doomsquadairsoft/d3vice-controlpoint-xbee/other/pics/guts.jpg

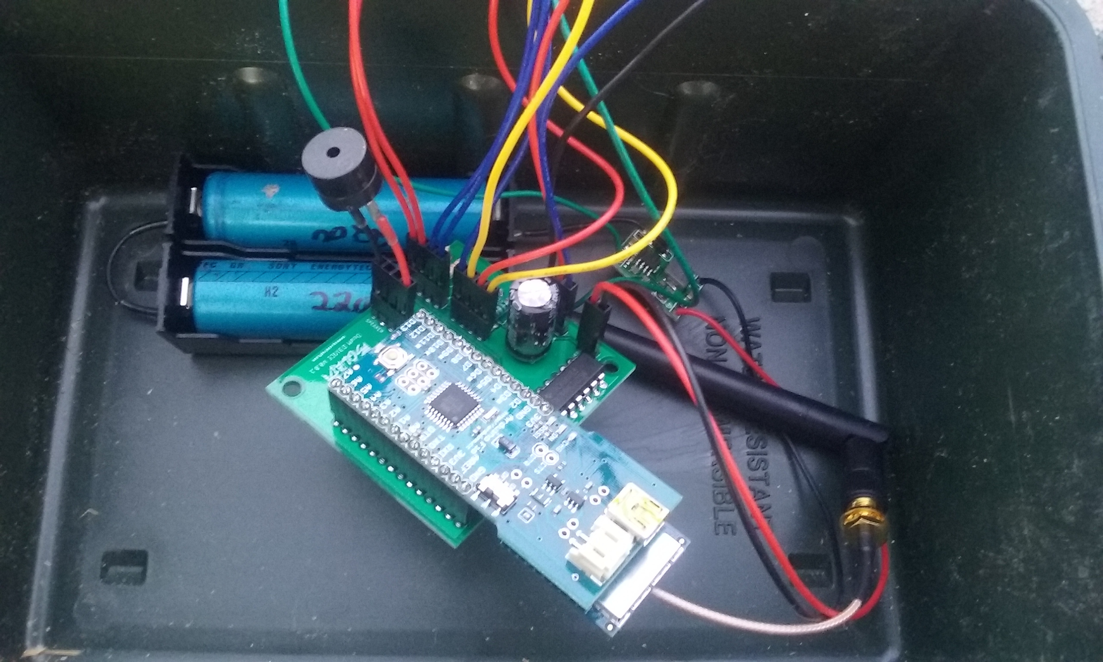
other/pics/guts.jpg
