doomsquadairsoft/d3vice-controlpoint-xbee/other/pics/pcb_yadda.png

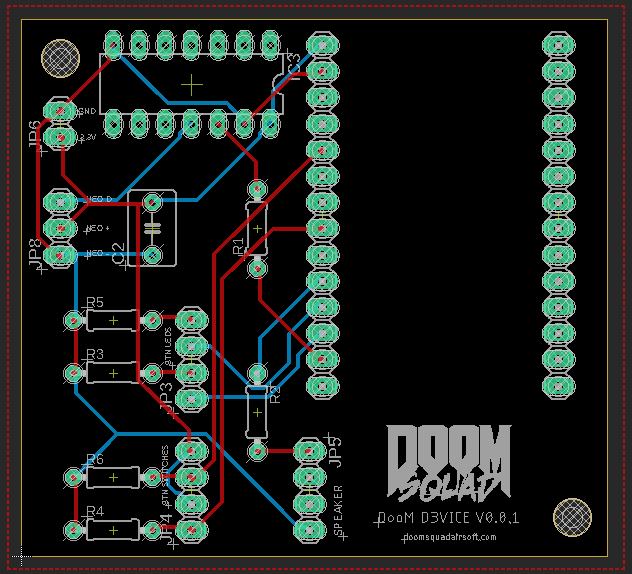
other/pics/pcb_yadda.png
