doomsquadairsoft/d3vice-controlpoint-xbee/other/pics/pcbtraces.png

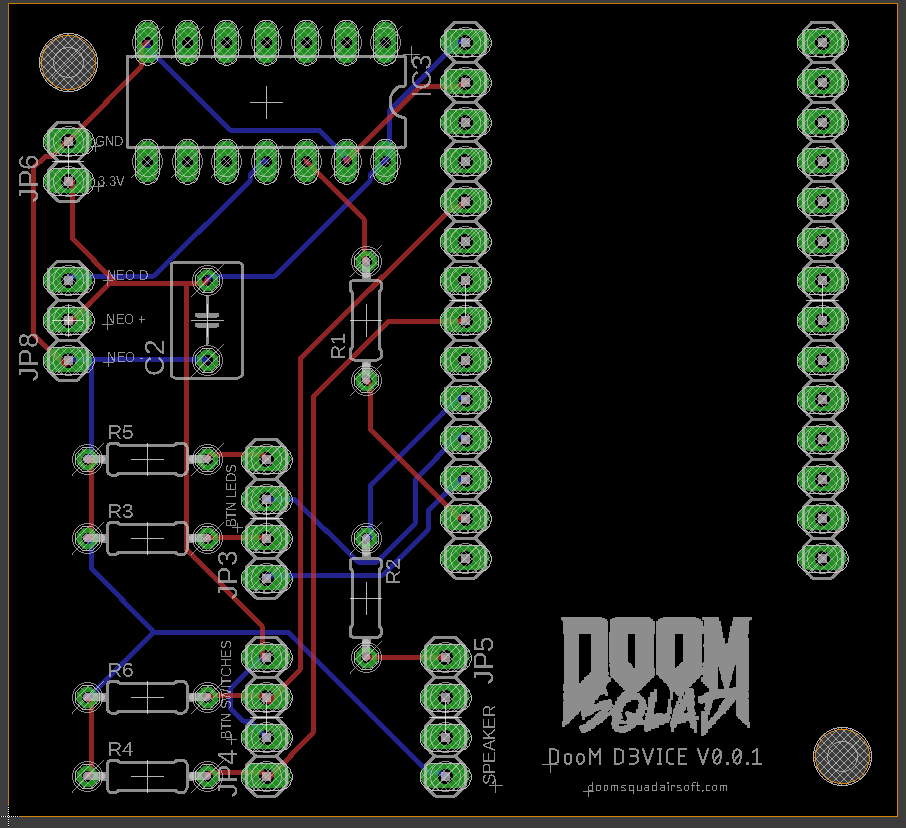
other/pics/pcbtraces.png
